kontur/motion-learning-prototype/processing/VideoTest/data/kinemata.jpg

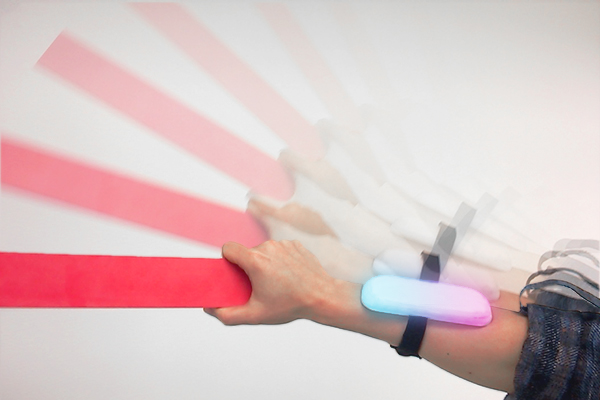
processing/VideoTest/data/kinemata.jpg
